MaciejKrysztowiak/POV_Display/POV_display_code/Core/Inc/img.h

#define IMG_SIZE 150

const uint8_t image[150][8] = {
{0b00000000, 0b00000000, 0b00000000, 0b00000000, 0b00000000, 0b00000000, 0b00000000, 0b00000000},
{0b00000000, 0b00000000, 0b00000000, 0b00000000, 0b00000000, 0b00000000, 0b00000000, 0b00000000},
{0b00000000, 0b00000000, 0b00000000, 0b00000000, 0b00000000, 0b00000000, 0b00000000, 0b00000000},
{0b00000000, 0b00000000, 0b00000000, 0b00000000, 0b00000000, 0b00000000, 0b00000000, 0b00000000},
{0b00000000, 0b00000000, 0b00000000, 0b00000000, 0b00000000, 0b00000000, 0b00000000, 0b00000000},
{0b00000000, 0b00000000, 0b00000000, 0b00000000, 0b00000000, 0b00000000, 0b00000000, 0b00000000},
{0b00000000, 0b00000000, 0b00000000, 0b00000000, 0b00000000, 0b00000000, 0b00000000, 0b00000000},
{0b00000000, 0b00000000, 0b00000000, 0b00000000, 0b00000000, 0b00000000, 0b00000000, 0b00000000},
{0b00000000, 0b00000000, 0b00000000, 0b00000000, 0b00000000, 0b00000000, 0b00000000, 0b00000000},
{0b00000000, 0b00000000, 0b00000000, 0b00000000, 0b00000000, 0b00000000, 0b00000000, 0b00000000},
{0b00000000, 0b00000000, 0b00000000, 0b00000000, 0b00000000, 0b00000000, 0b00000000, 0b00000000},
{0b00000000, 0b00000000, 0b00000000, 0b00000000, 0b00000000, 0b00000000, 0b00000000, 0b00000000},
{0b00000000, 0b00000000, 0b00000000, 0b00000000, 0b00000000, 0b00000000, 0b00000000, 0b00000000},
{0b00000000, 0b00000000, 0b00000000, 0b00000000, 0b00000000, 0b00000000, 0b00000000, 0b00000000},
{0b01001000, 0b10010010, 0b00100101, 0b00001000, 0b00000000, 0b00000000, 0b00000000, 0b00000000},
{0b00000000, 0b10010000, 0b00000001, 0b00001000, 0b00000000, 0b00000000, 0b00000000, 0b00000000},
{0b00000000, 0b00010000, 0b00000001, 0b00001000, 0b00000000, 0b00000000, 0b00000000, 0b00000000},
{0b00000000, 0b10010000, 0b00000001, 0b00000000, 0b00000000, 0b00000000, 0b00000000, 0b00000000},
{0b00000000, 0b10000000, 0b00100101, 0b00000000, 0b00000000, 0b00000000, 0b00000000, 0b00000000},
{0b00000000, 0b00000000, 0b00000000, 0b00000000, 0b00000000, 0b00000000, 0b00000000, 0b00000000},
{0b00000000, 0b10010000, 0b00000000, 0b00000000, 0b00000000, 0b00000000, 0b00000000, 0b00000000},
{0b01000000, 0b10010010, 0b00100101, 0b00000000, 0b00000000, 0b00000000, 0b00000000, 0b00000000},
{0b01001000, 0b00000000, 0b00100001, 0b00000000, 0b00000000, 0b00000000, 0b00000000, 0b00000000},
{0b00001000, 0b00000000, 0b00000001, 0b00001000, 0b00000000, 0b00000000, 0b00000000, 0b00000000},
{0b00001000, 0b00000000, 0b00000001, 0b00001000, 0b00000000, 0b00000000, 0b00000000, 0b00000000},
{0b00001000, 0b00000000, 0b00000001, 0b00000000, 0b00000000, 0b00000000, 0b00000000, 0b00000000},
{0b01000000, 0b00000010, 0b00100101, 0b00000000, 0b00000000, 0b00000000, 0b00000000, 0b00000000},
{0b00000000, 0b10010010, 0b00100100, 0b00000000, 0b00000000, 0b00000000, 0b00000000, 0b00000000},
{0b00000000, 0b00000000, 0b00000000, 0b00000000, 0b00000000, 0b00000000, 0b00000000, 0b00000000},
{0b00000000, 0b00000000, 0b00100001, 0b00001000, 0b00000000, 0b00000000, 0b00000000, 0b00000000},
{0b00000000, 0b10010000, 0b00100100, 0b00000000, 0b00000000, 0b00000000, 0b00000000, 0b00000000},
{0b01001000, 0b10010010, 0b00000000, 0b00000000, 0b00000000, 0b00000000, 0b00000000, 0b00000000},
{0b01001000, 0b00000000, 0b00000000, 0b00000000, 0b00000000, 0b00000000, 0b00000000, 0b00000000},
{0b01000000, 0b10010010, 0b00000000, 0b00000000, 0b00000000, 0b00000000, 0b00000000, 0b00000000},
{0b00000000, 0b10000000, 0b00100101, 0b00000000, 0b00000000, 0b00000000, 0b00000000, 0b00000000},
{0b00000000, 0b00000000, 0b00000001, 0b00001000, 0b00000000, 0b00000000, 0b00000000, 0b00000000},
{0b00000000, 0b00000000, 0b00000000, 0b00000000, 0b00000000, 0b00000000, 0b00000000, 0b00000000},
{0b00000000, 0b00000000, 0b00000000, 0b00000000, 0b00000000, 0b00000000, 0b00000000, 0b00000000},
{0b00000000, 0b00000000, 0b00000000, 0b00000000, 0b00000000, 0b00000000, 0b00000000, 0b00000000},
{0b00000000, 0b00000000, 0b00000000, 0b00000000, 0b00000000, 0b00000000, 0b00000000, 0b00000000},
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
};
